propane-and-electrons/hadokenIMU/hardware/hadokenIMU.sch

## KiCad design hardware/hadokenIMU.sch (2013-04-01)

Schematic: hadokenIMU.sch

Parts:
C1, C4: 22pF; SM0805
C2, C6, C9: 0.1uF; SM0805
C3: 1uF; SM0805
C5, C8: 4.7uF; SM0805
C7: 10uF; SM0805
C10: 2.2nF; SM0805
D1: GF1A; DO214
D2: CHARGE; SM0805
J1: USBMINI; USB-M26FTR
M1: WIFLY; XBEE-SMD
P1: 5V; SIL-2
P2: BATT; JST-2-SMD
P3: BUTTON; SIL-2
P4: CONN_3X2; ICSP_PADS
P5: BATTPTH; SIL-2
R1, R2: 22; SM0805
R3: 470; SM0805
R4, R6: 10k; SM0805
R5: 2k; SM0805
R7, R8: 4.7k; SM0805
SW1: SPDT; CL-SB-12A
TH1: 0ZCB0050FF2G; SM1210
U1: ATMEGA32U4; TQFP44
U2: MIC5265; TSOT23-5
U3: MCP73831; SOT23-5
U4: MPU-9150; QFN24
X1: NX5032GA
